Rouble/senior-project/H-bridge board/2013-01-09 15.14.08.jpg

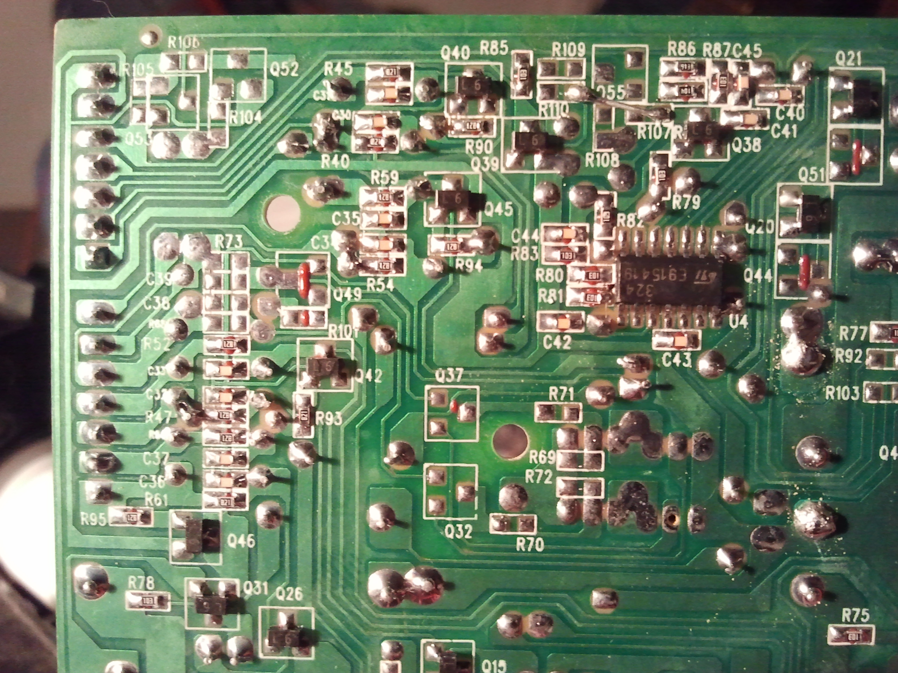
H-bridge board/2013-01-09 15.14.08.jpg
