Rouble/senior-project/H-bridge board/2013-01-09 15.17.00.jpg

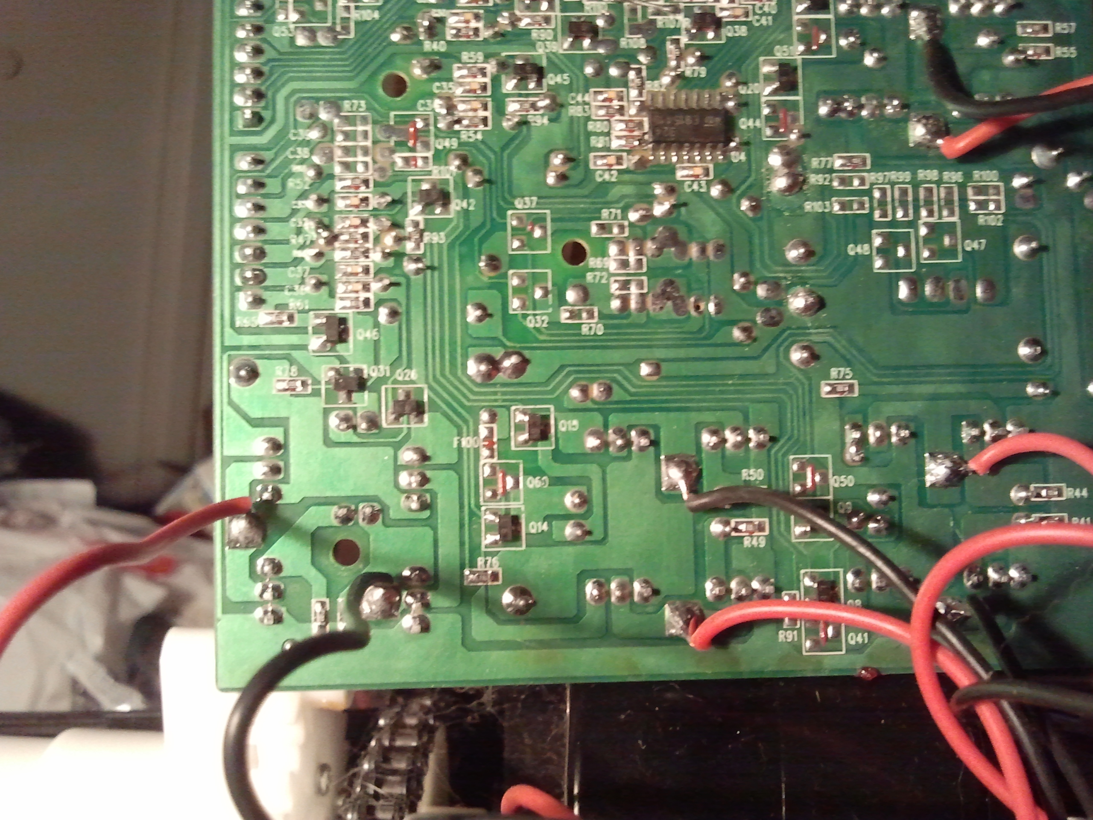
H-bridge board/2013-01-09 15.17.00.jpg
